aditisjoshi/dankherb/finalCadAndCutFiles/render.JPG

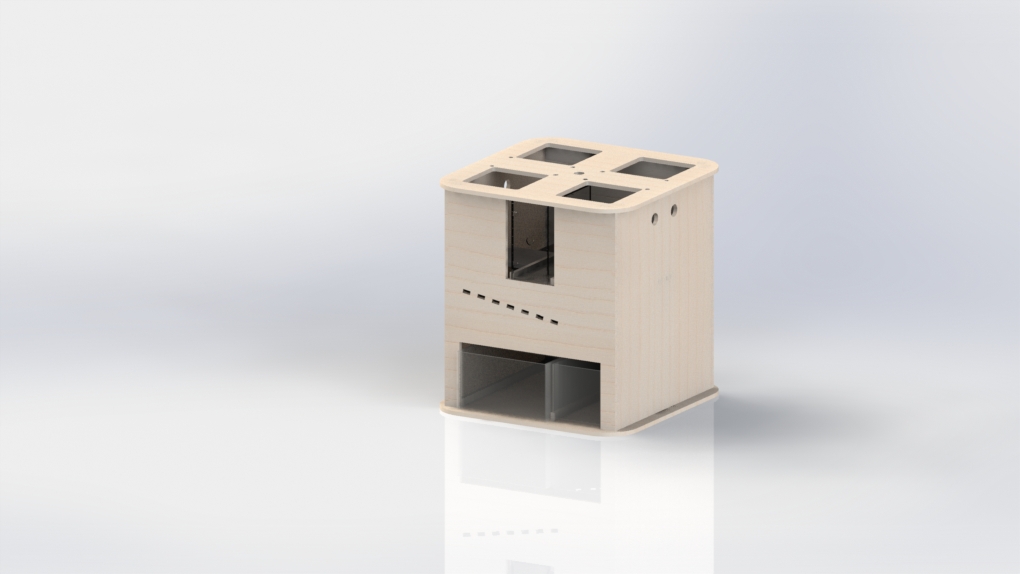
finalCadAndCutFiles/render.JPG
