aditisjoshi/dankherb/sun.png

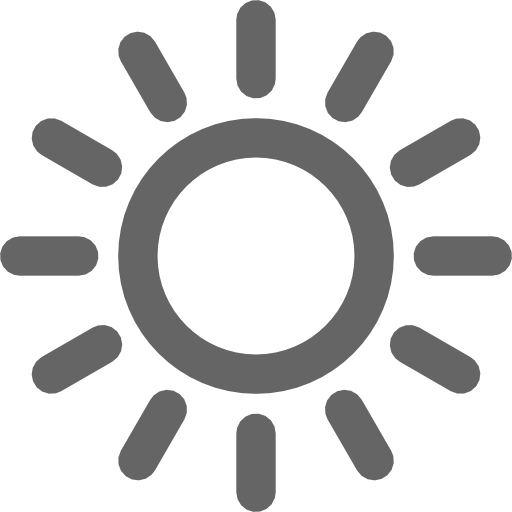
sun.png
