aditisjoshi/dankherb/water.png

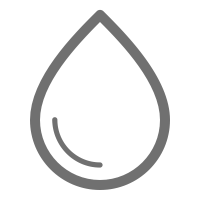
water.png
