aditisjoshi/dankherb/website/images/2sateAaron.png

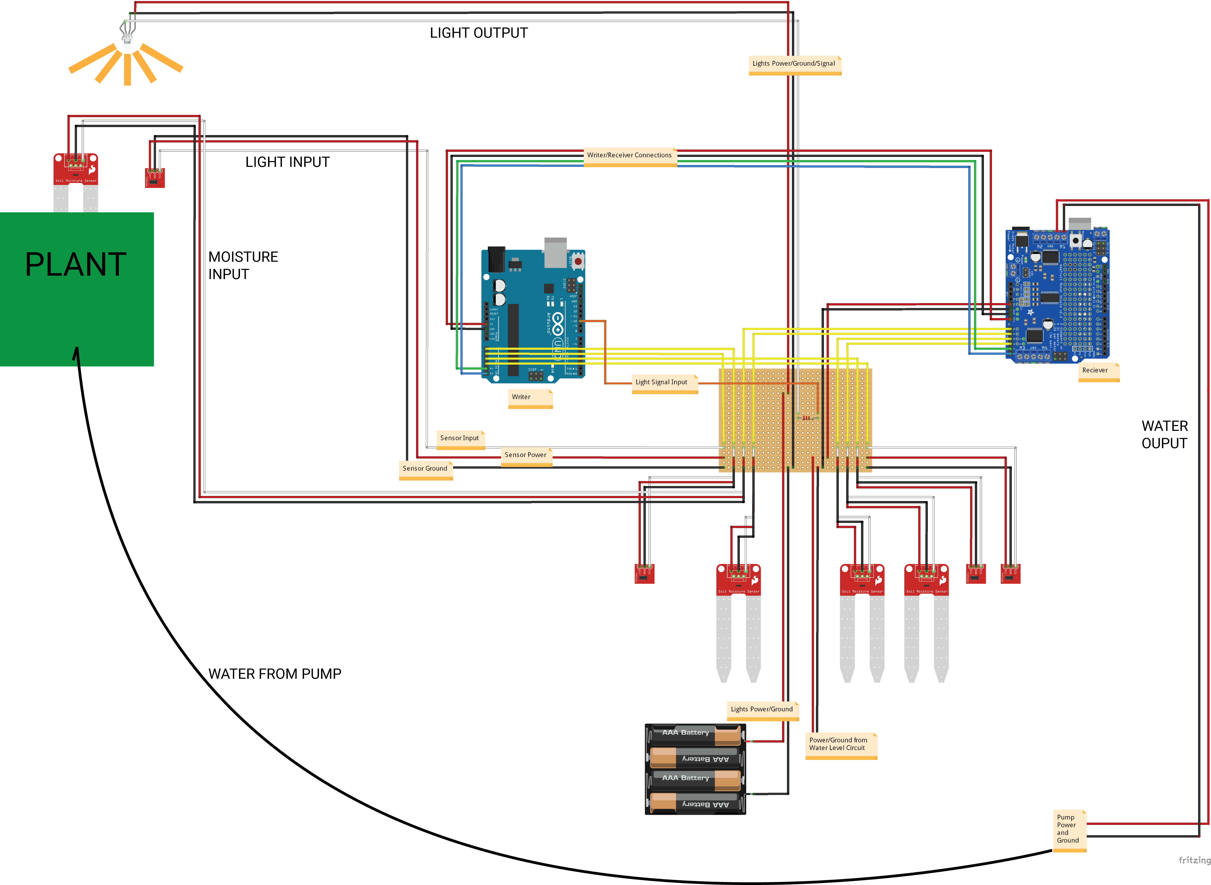
website/images/2sateAaron.png
