aditisjoshi/dankherb/website/images/acrylicboxes.jpg

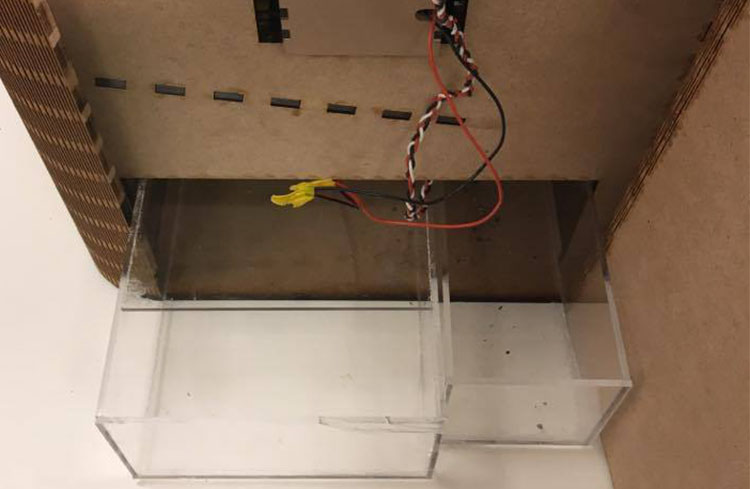
website/images/acrylicboxes.jpg
