aditisjoshi/dankherb/website/images/aditiphoto.JPG

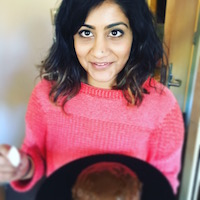
website/images/aditiphoto.JPG
