aditisjoshi/dankherb/website/images/arduinos.jpg

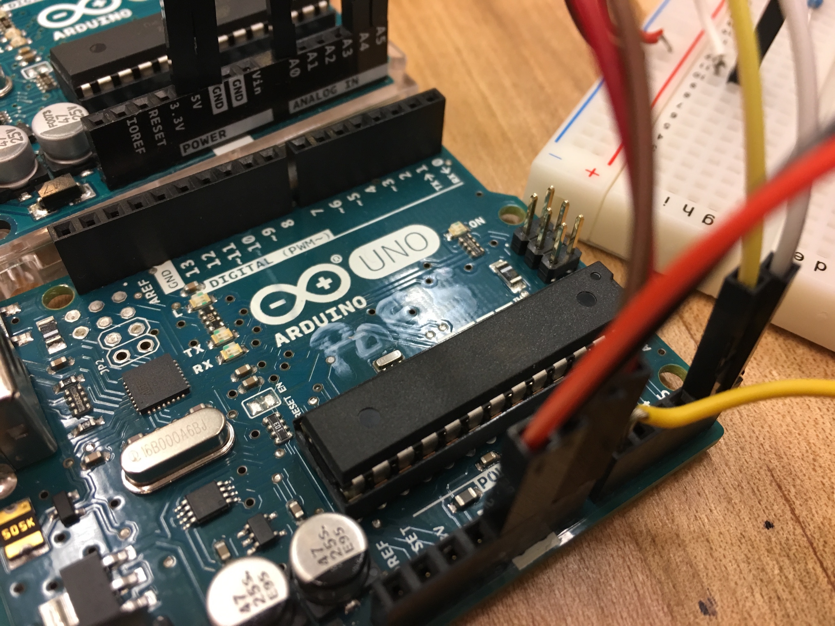
website/images/arduinos.jpg
