aditisjoshi/dankherb/website/images/gallery1.JPG

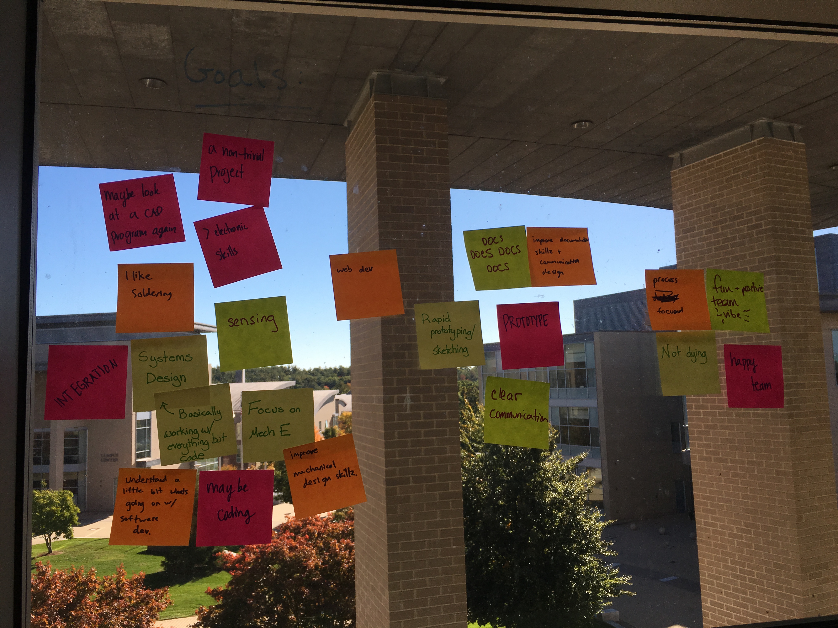
website/images/gallery1.JPG
