aditisjoshi/dankherb/website/images/gallery2.JPG

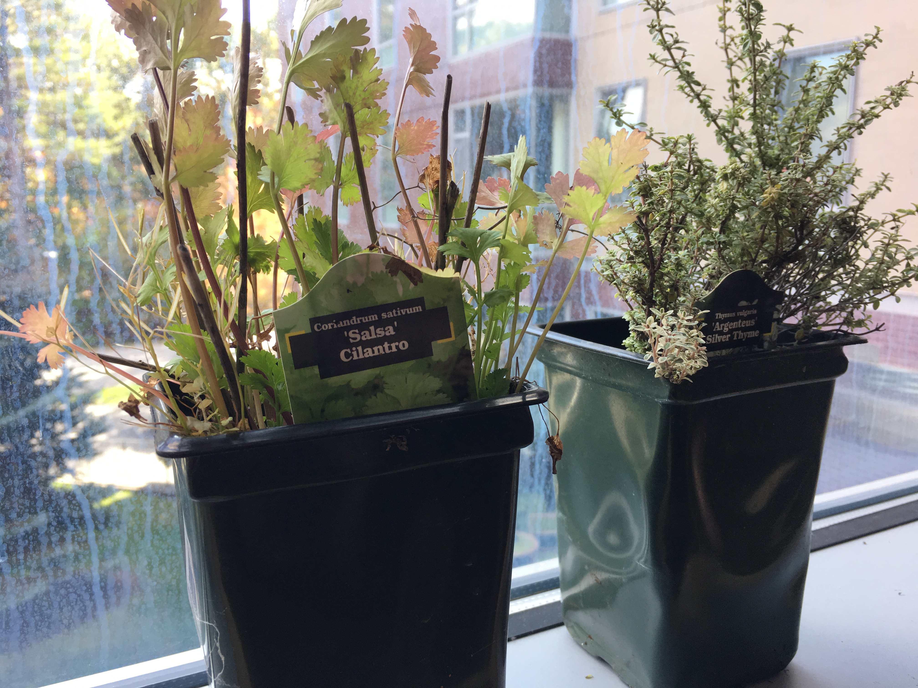
website/images/gallery2.JPG
