aditisjoshi/dankherb/website/images/gallery4.JPG

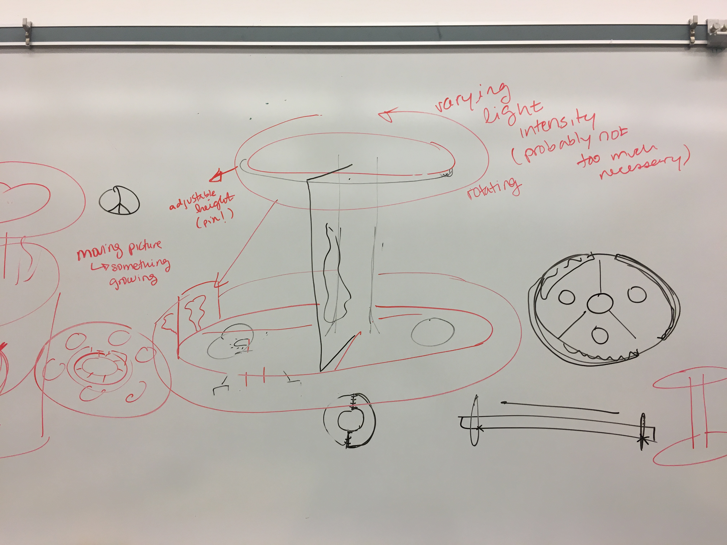
website/images/gallery4.JPG
