aditisjoshi/dankherb/website/images/gallery5.JPG

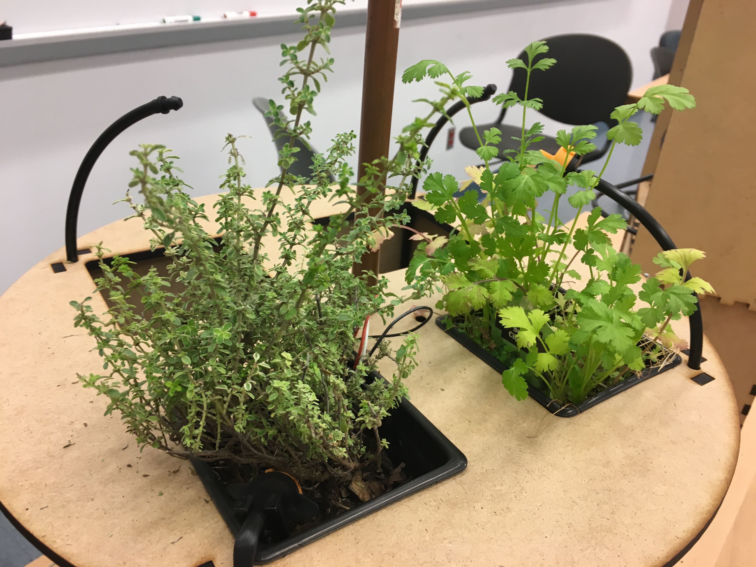
website/images/gallery5.JPG
