aditisjoshi/dankherb/website/images/gallery6.JPG

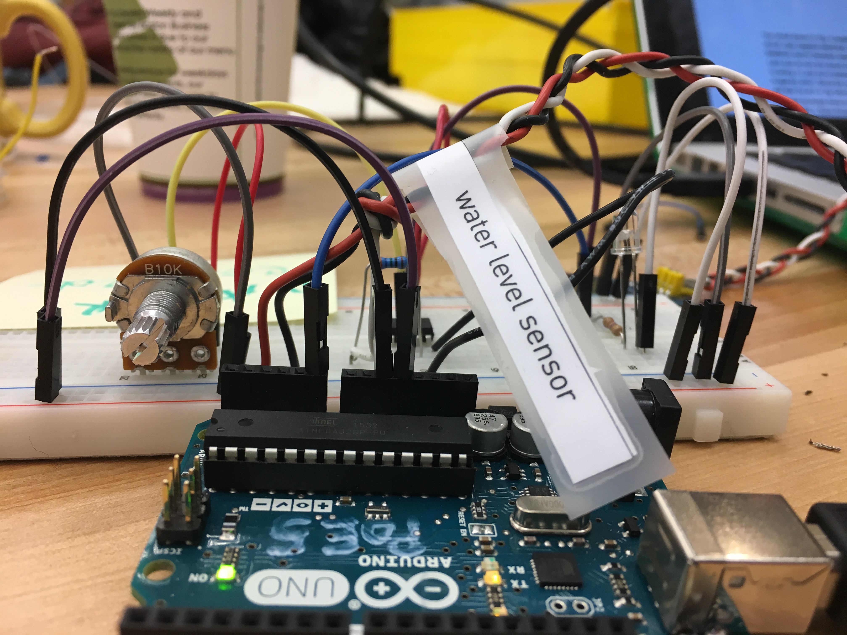
website/images/gallery6.JPG
