aditisjoshi/dankherb/website/images/gallery8.jpg

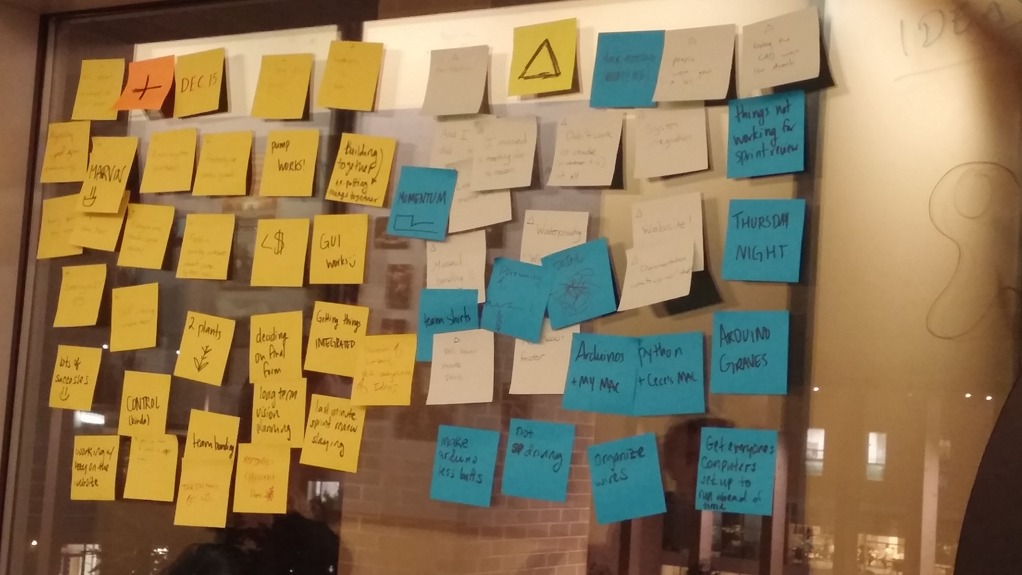
website/images/gallery8.jpg
