aditisjoshi/dankherb/website/images/gallery9.jpg

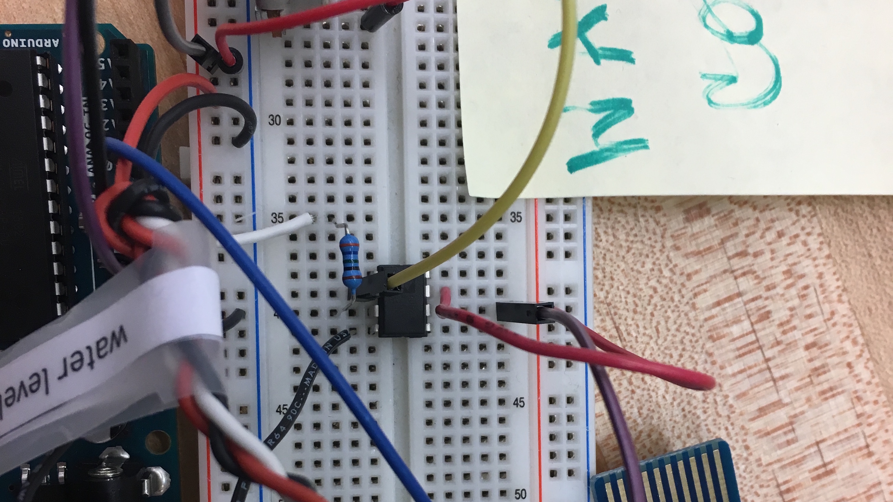
website/images/gallery9.jpg
