aditisjoshi/dankherb/website/images/gallery11.JPG

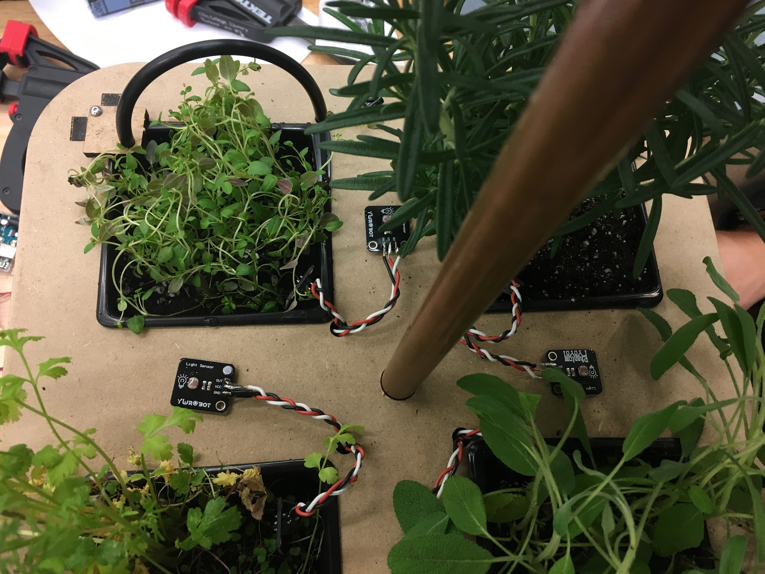
website/images/gallery11.JPG
