aditisjoshi/dankherb/website/images/gallery12.JPG

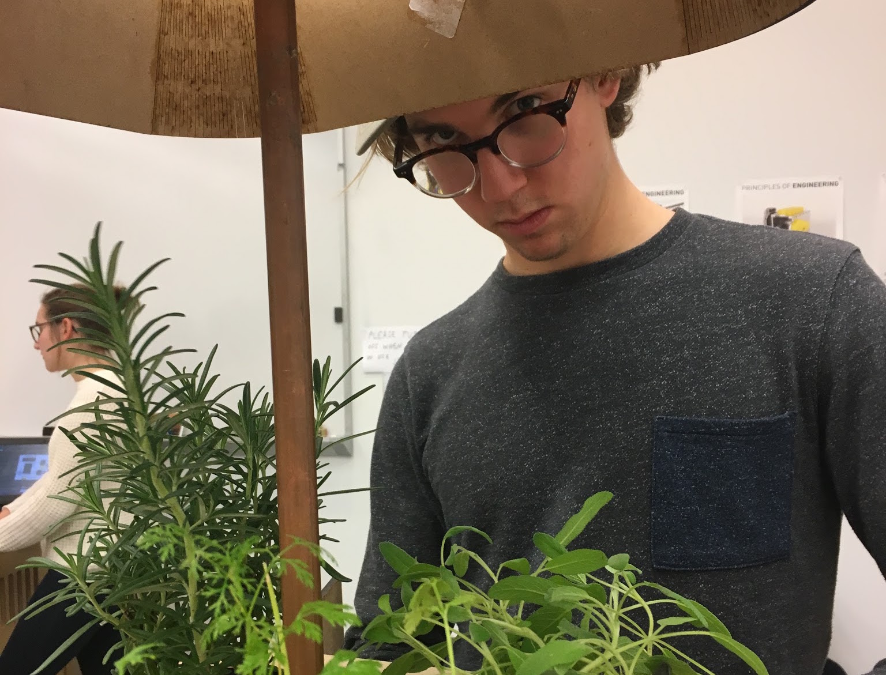
website/images/gallery12.JPG
