aditisjoshi/dankherb/website/images/gallery13.JPG

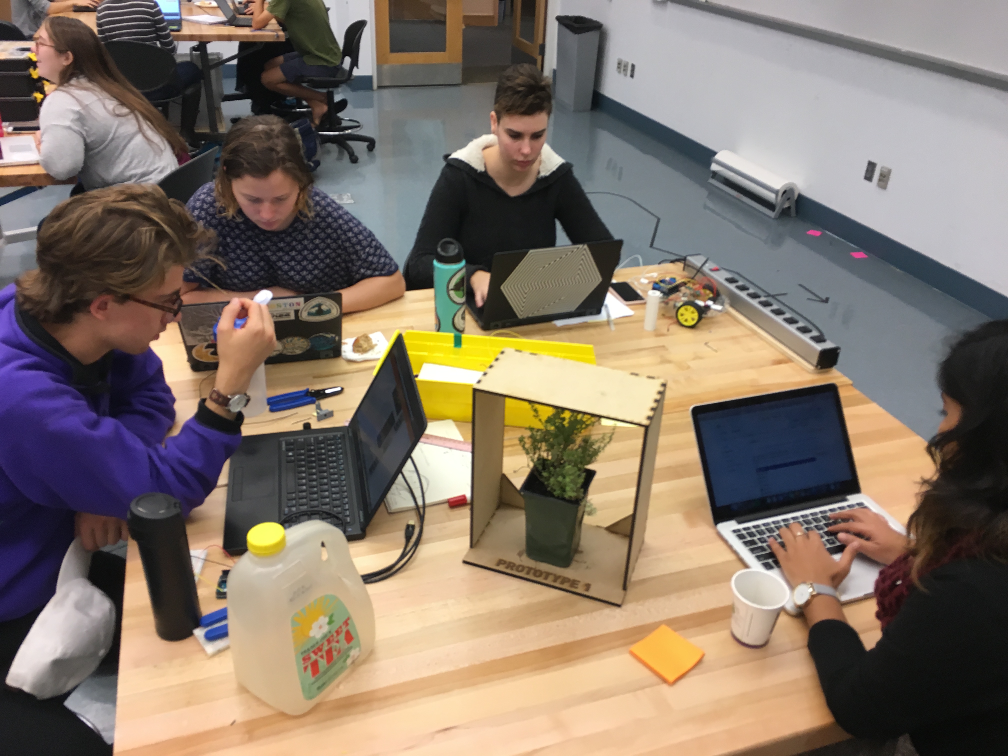
website/images/gallery13.JPG
