aditisjoshi/dankherb/website/images/gallery14.JPG

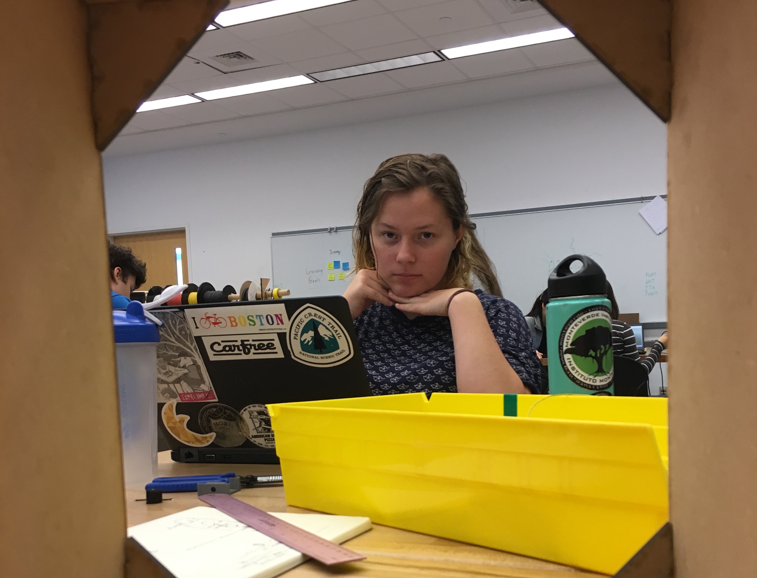
website/images/gallery14.JPG
