aditisjoshi/dankherb/website/images/gallery15.JPG

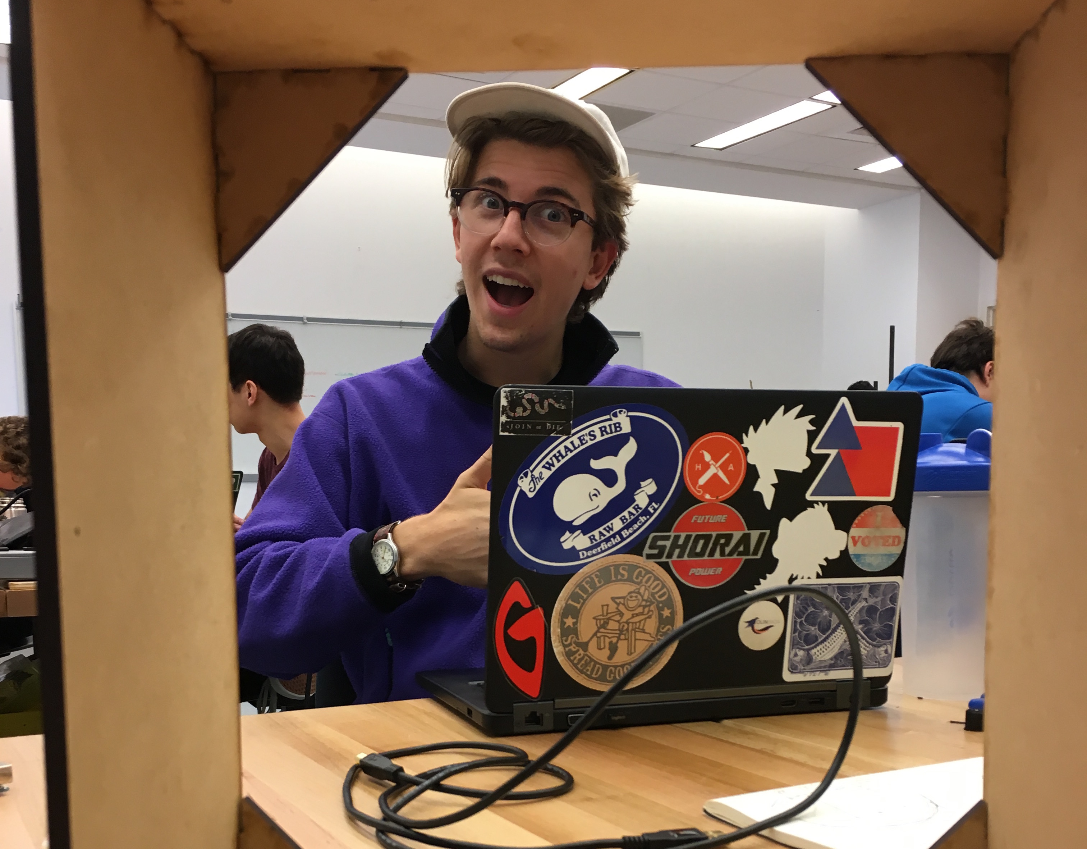
website/images/gallery15.JPG
