aditisjoshi/dankherb/website/images/gallery16.JPG

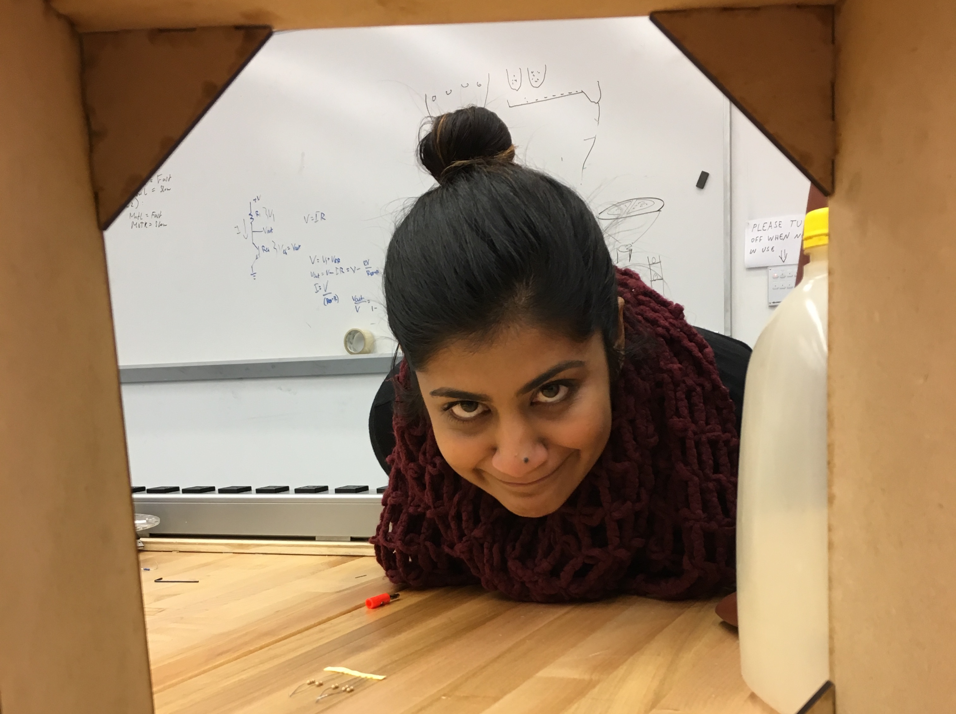
website/images/gallery16.JPG
