aditisjoshi/dankherb/website/images/gallery17.JPG

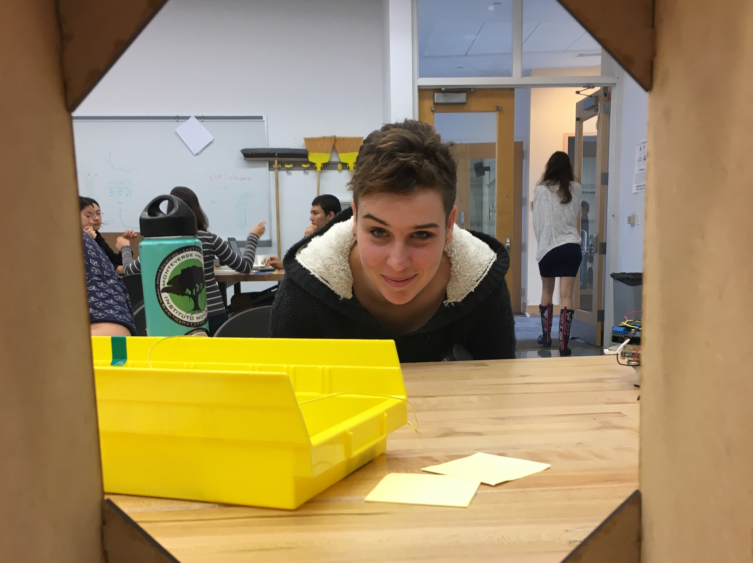
website/images/gallery17.JPG
