aditisjoshi/dankherb/website/images/gallery18.JPG

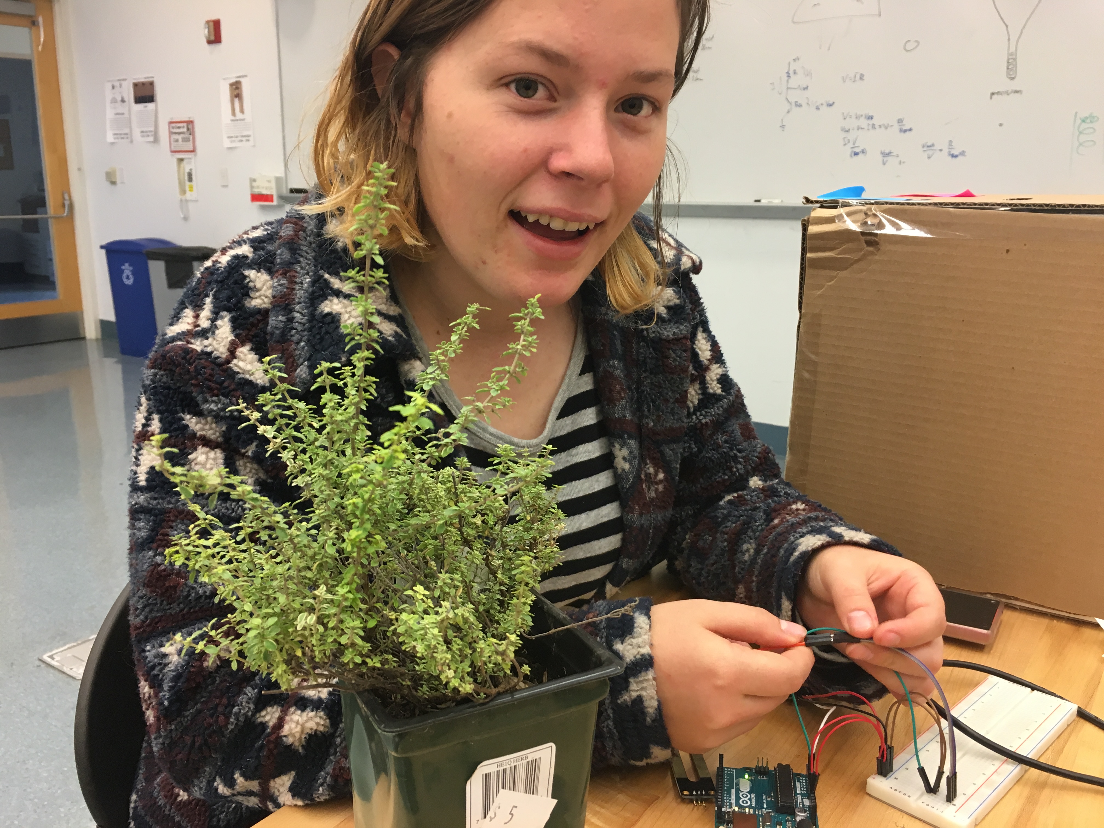
website/images/gallery18.JPG
