aditisjoshi/dankherb/website/images/gallery19.JPG

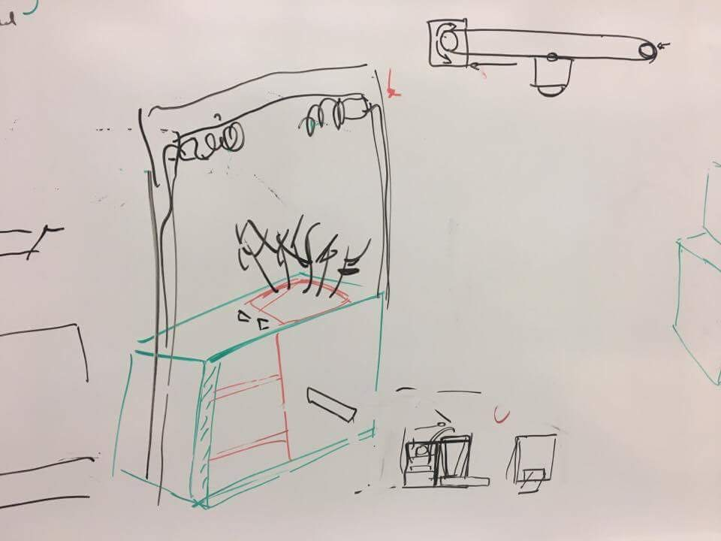
website/images/gallery19.JPG
