aditisjoshi/dankherb/website/images/gallery20.JPG

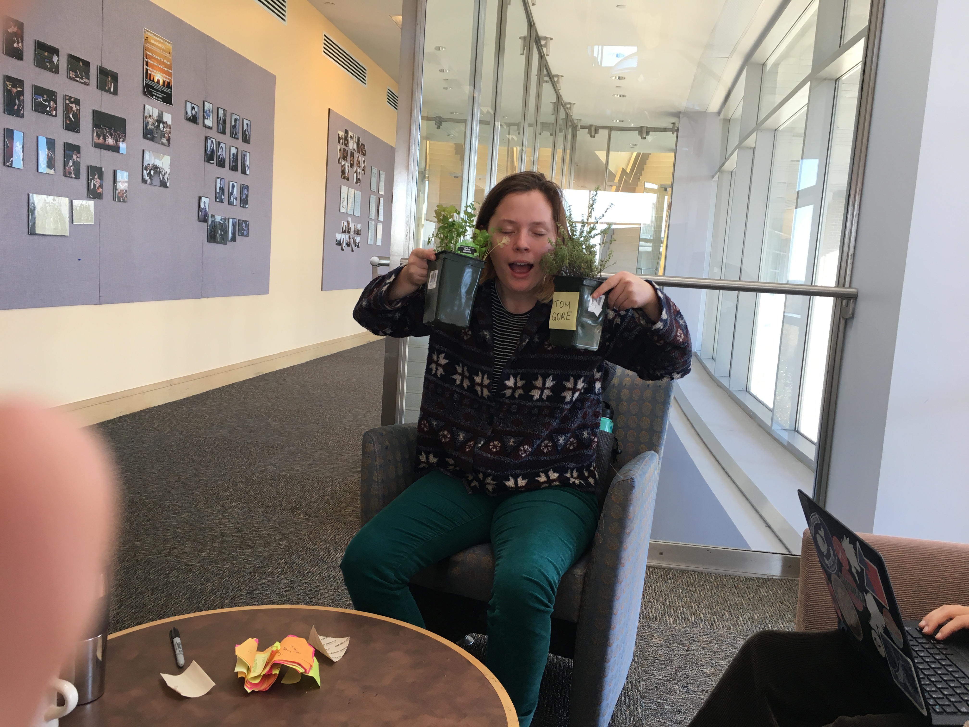
website/images/gallery20.JPG
