aditisjoshi/dankherb/website/images/harperphoto.jpg

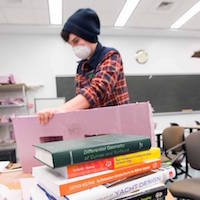
website/images/harperphoto.jpg
