aditisjoshi/dankherb/website/images/hero_image.jpg

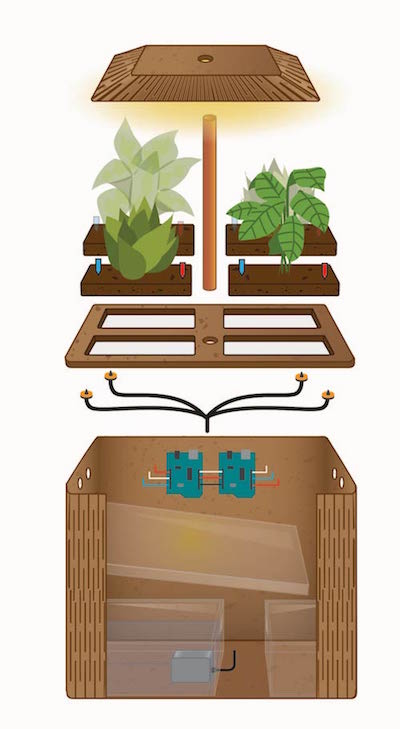
website/images/hero_image.jpg
