aditisjoshi/dankherb/website/images/HeroImageWithCallouts.png

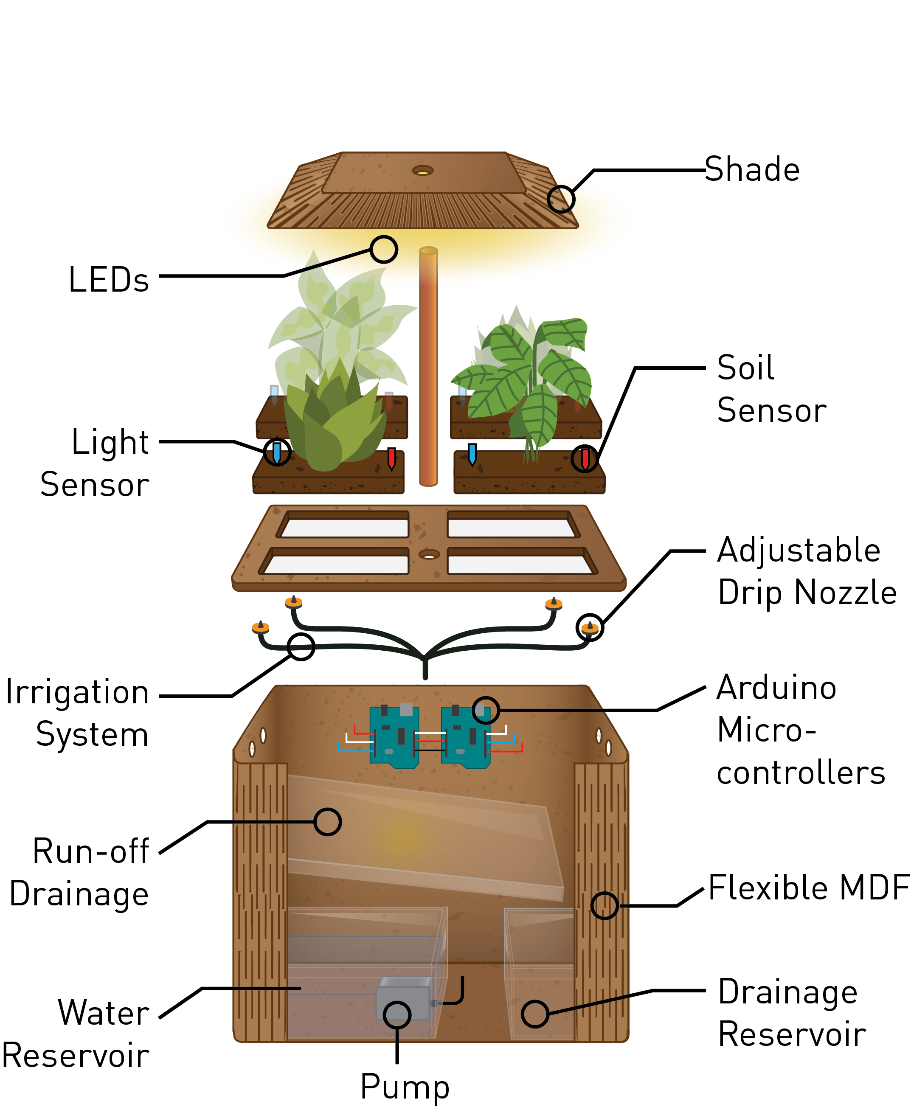
website/images/HeroImageWithCallouts.png
