aditisjoshi/dankherb/website/images/izzyphoto.jpg

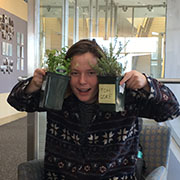
website/images/izzyphoto.jpg
