aditisjoshi/dankherb/website/images/johnphoto.JPG

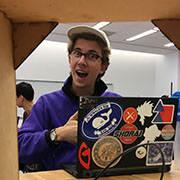
website/images/johnphoto.JPG
