aditisjoshi/dankherb/website/images/mech1.png

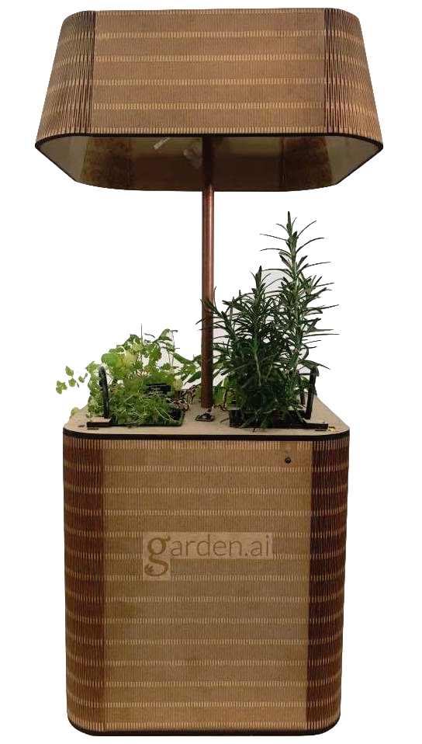
website/images/mech1.png
