aditisjoshi/dankherb/website/images/pump.jpg

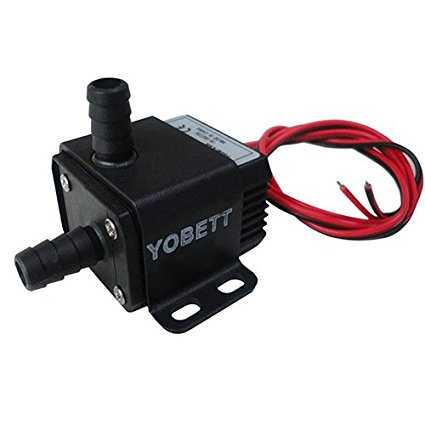
website/images/pump.jpg
