aditisjoshi/dankherb/website/images/python_code.png

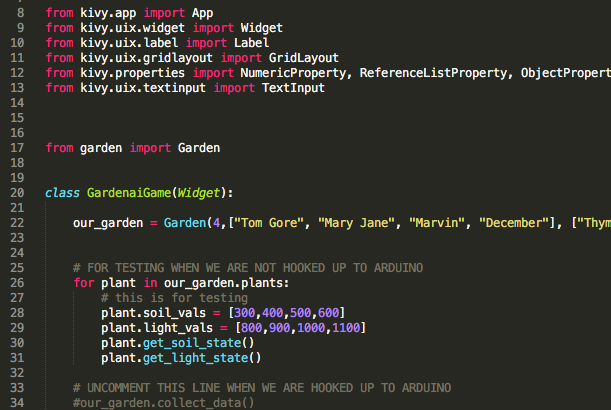
website/images/python_code.png
