aditisjoshi/dankherb/website/images/sprint1.JPG

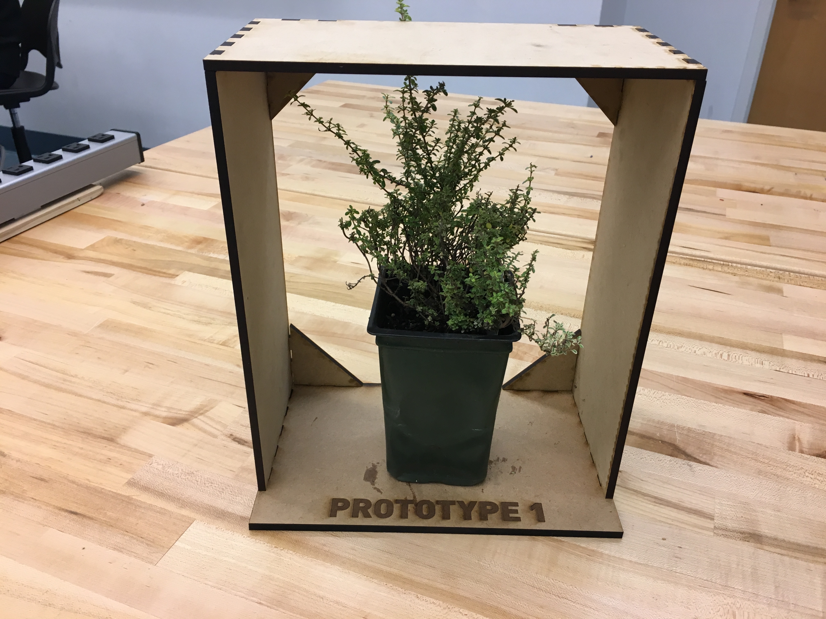
website/images/sprint1.JPG
