aditisjoshi/dankherb/website/images/sprint2.JPG

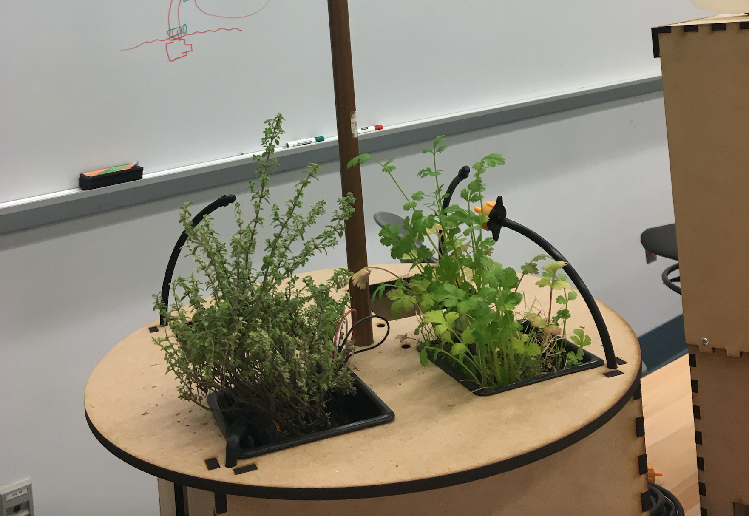
website/images/sprint2.JPG
