aditisjoshi/dankherb/website/images/sprint3.JPG

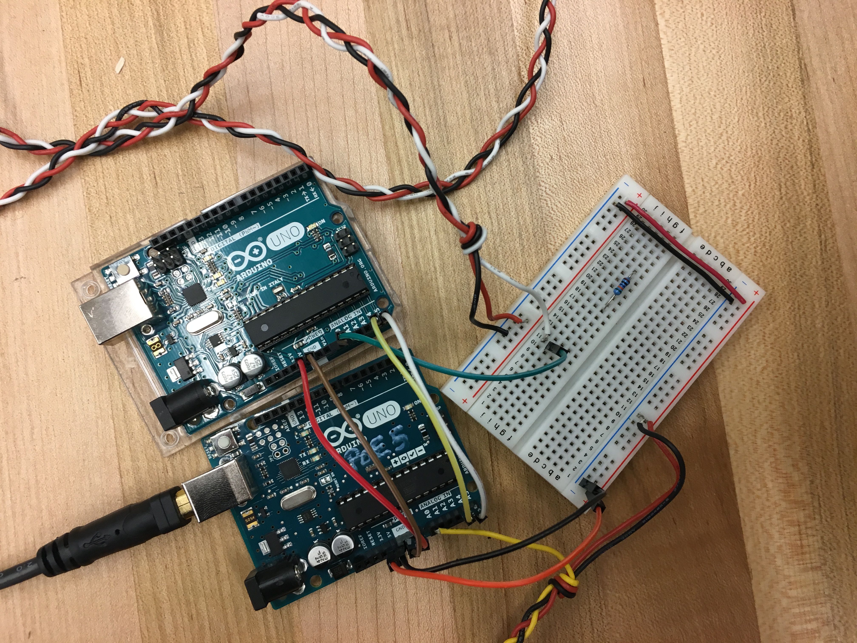
website/images/sprint3.JPG
