aditisjoshi/dankherb/website/images/sprint4.jpg

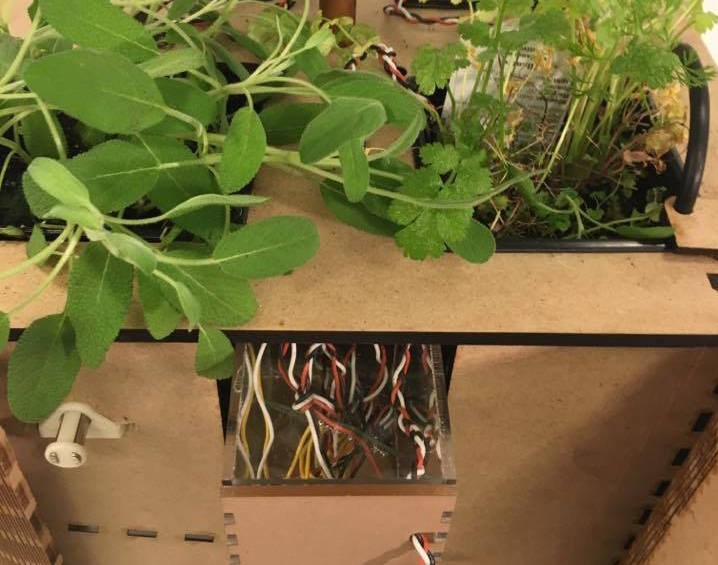
website/images/sprint4.jpg
