aditisjoshi/dankherb/website/images/water_level_sensor.jpg

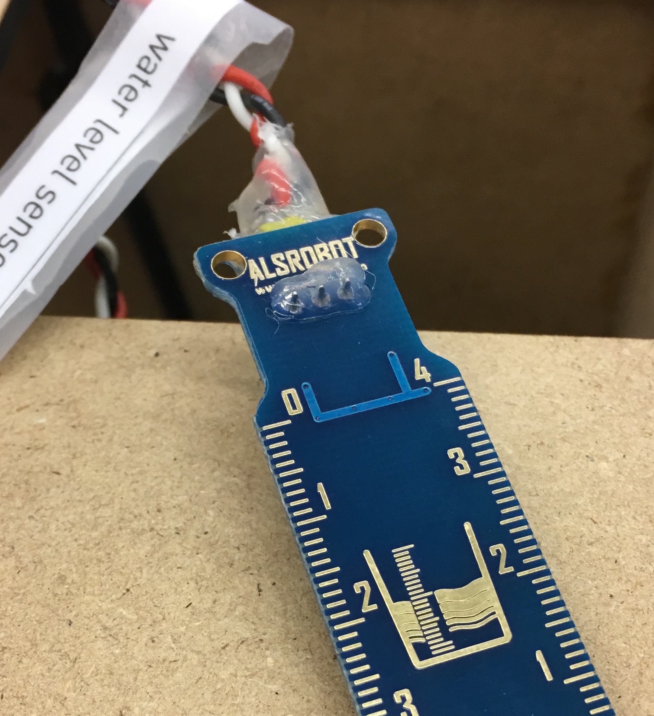
website/images/water_level_sensor.jpg
