aditisjoshi/dankherb/website/images/waterlevelCircuit.jpg

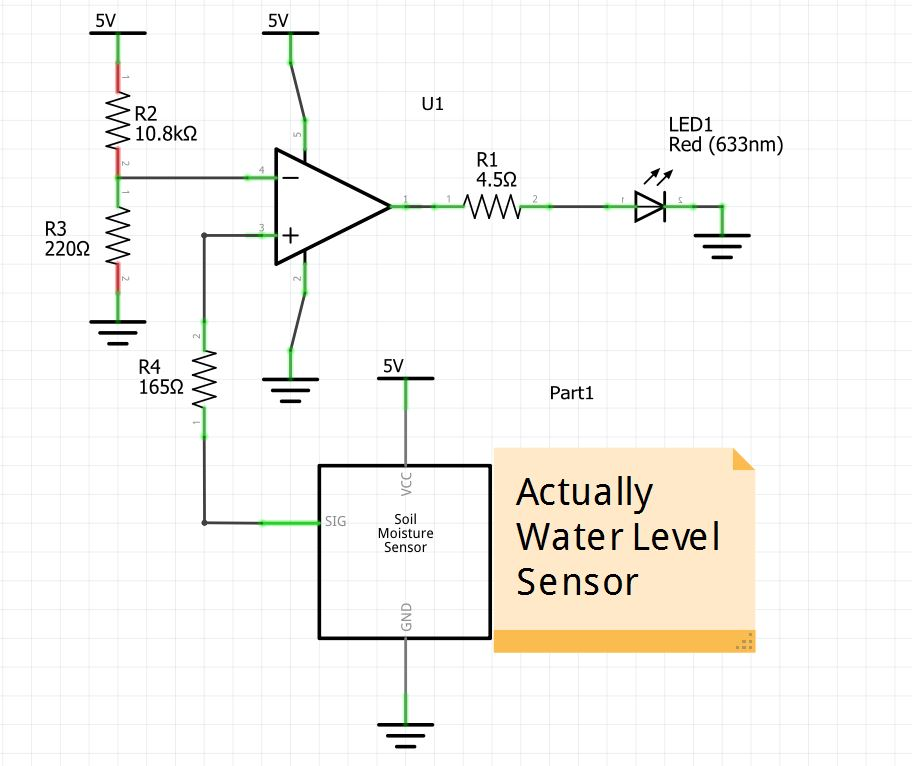
website/images/waterlevelCircuit.jpg
