aditisjoshi/dankherb/finalCadAndCutFiles/electronicsbox/elecback.SLDPRT

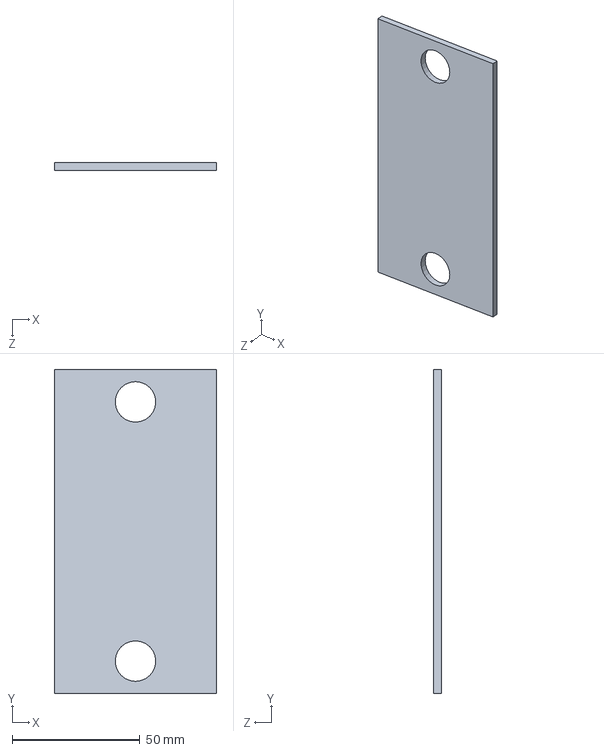
[picture p59: CAD file, 2016-12-13]
finalCadAndCutFiles/electronicsbox/elecback.SLDPRT
63.5 x 127.0 x 3.00 mm
