aditisjoshi/dankherb/finalCadAndCutFiles/main cut sheets/1_4mdf2.DXF

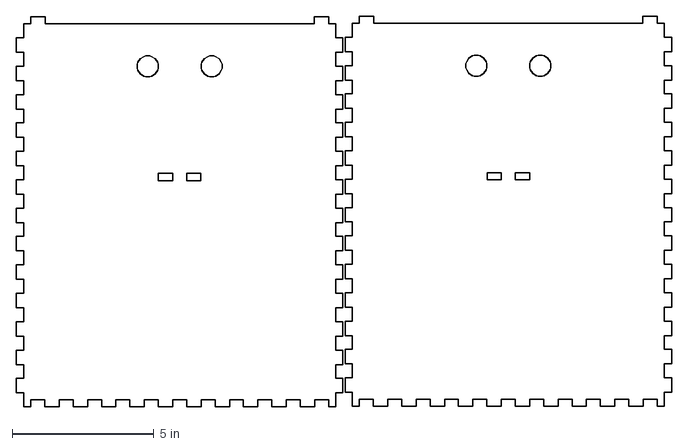
[picture p60: CAD file, 2016-12-13]
finalCadAndCutFiles/main cut sheets/1_4mdf2.DXF
23.1 x 13.8 in
