aditisjoshi/dankherb/finalCadAndCutFiles/ramp.SLDPRT

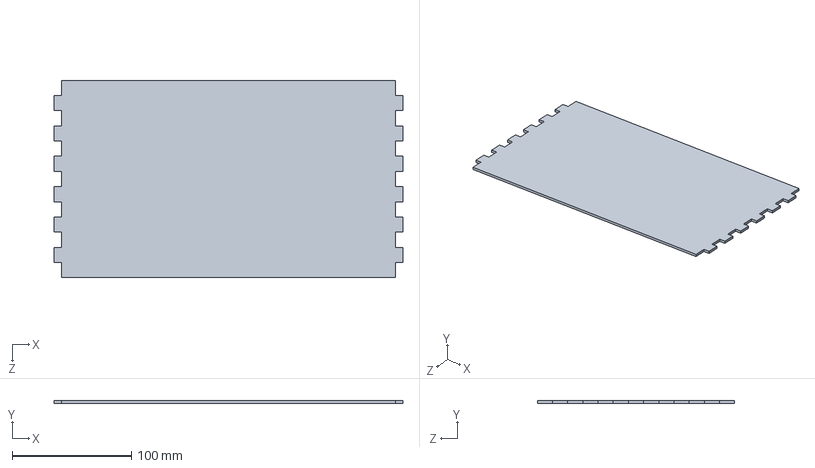
[picture p61: CAD file, 2016-12-13]
finalCadAndCutFiles/ramp.SLDPRT
292.1 x 2.54 x 165.1 mm
