aditisjoshi/dankherb/finalCadAndCutFiles/backpanel.SLDPRT

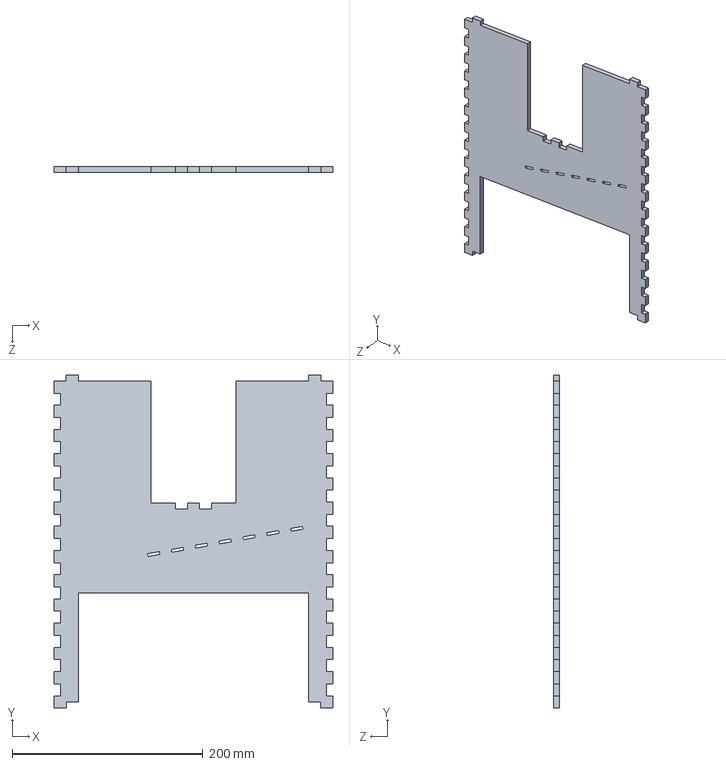
[picture p62: CAD file, 2016-12-13]
finalCadAndCutFiles/backpanel.SLDPRT
292.1 x 349.2 x 6.35 mm
