aditisjoshi/dankherb/finalCadAndCutFiles/drainageresovoir/drbottom.SLDPRT

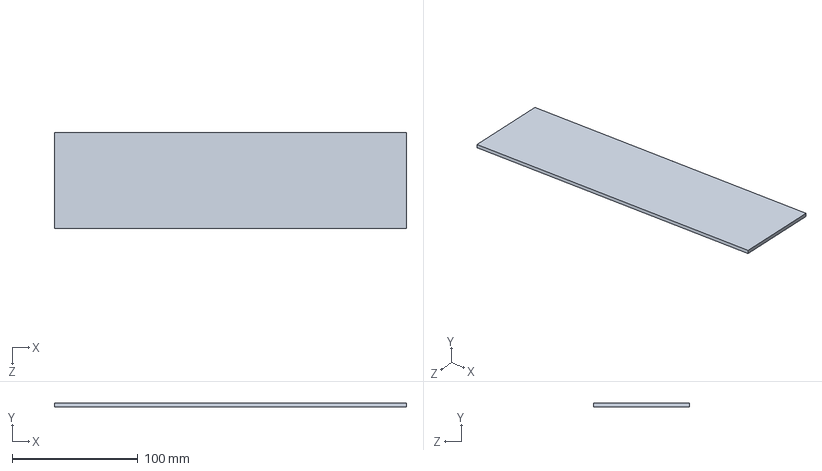
[picture p63: CAD file, 2016-12-13]
finalCadAndCutFiles/drainageresovoir/drbottom.SLDPRT
279.8 x 3.00 x 76.6 mm
