aditisjoshi/dankherb/finalCadAndCutFiles/main cut sheets/118AcrylicRampAndBox.DXF

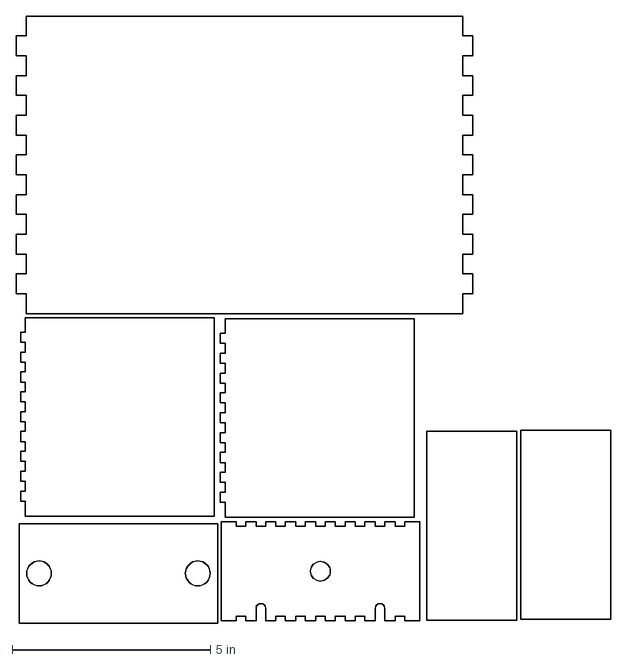
[picture p64: CAD file, 2016-12-13]
finalCadAndCutFiles/main cut sheets/118AcrylicRampAndBox.DXF
15.0 x 15.3 in
