aditisjoshi/dankherb/finalCadAndCutFiles/pump resovoir/waterbottom2.SLDPRT

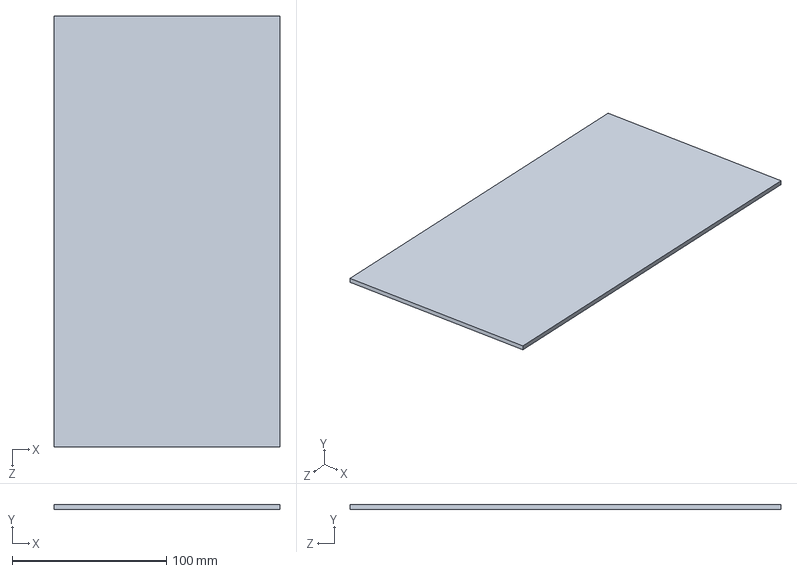
[picture p65: CAD file, 2016-12-13]
finalCadAndCutFiles/pump resovoir/waterbottom2.SLDPRT
146.4 x 3.00 x 279.8 mm
