aditisjoshi/dankherb/finalCadAndCutFiles/electronicsbox/elecbottom.SLDPRT

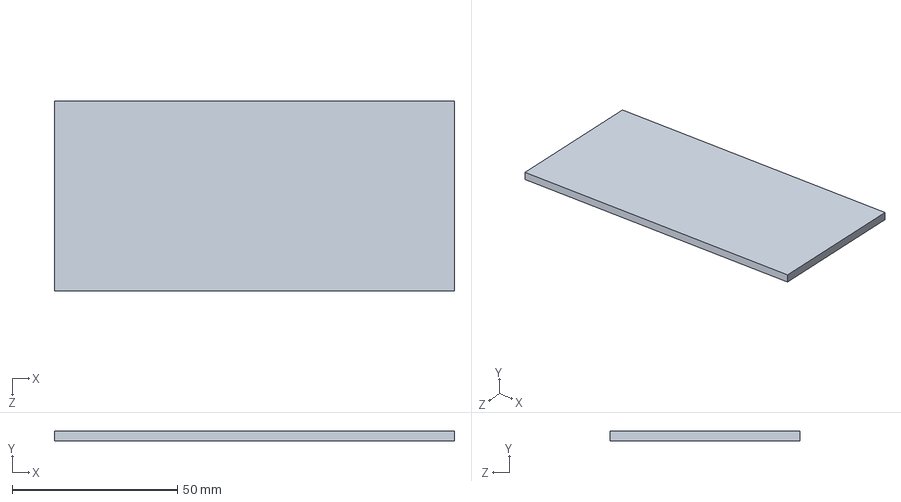
[picture p66: CAD file, 2016-12-13]
finalCadAndCutFiles/electronicsbox/elecbottom.SLDPRT
121.0 x 3.00 x 57.5 mm
