aditisjoshi/dankherb/finalCadAndCutFiles/lightmount.SLDPRT

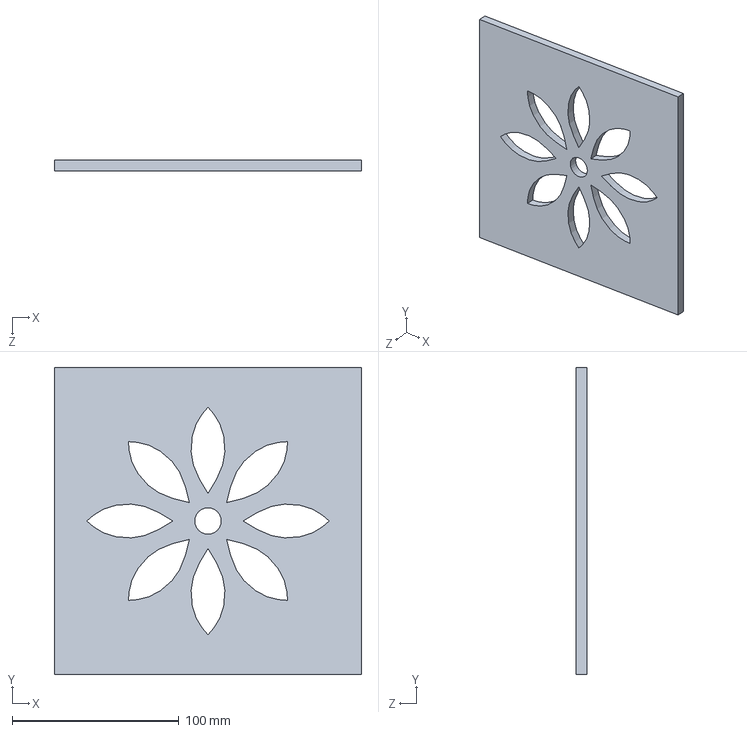
[picture p67: CAD file, 2016-12-13]
finalCadAndCutFiles/lightmount.SLDPRT
184.1 x 184.1 x 6.35 mm
