aditisjoshi/dankherb/finalCadAndCutFiles/main cut sheets/1_4mdf4.DXF

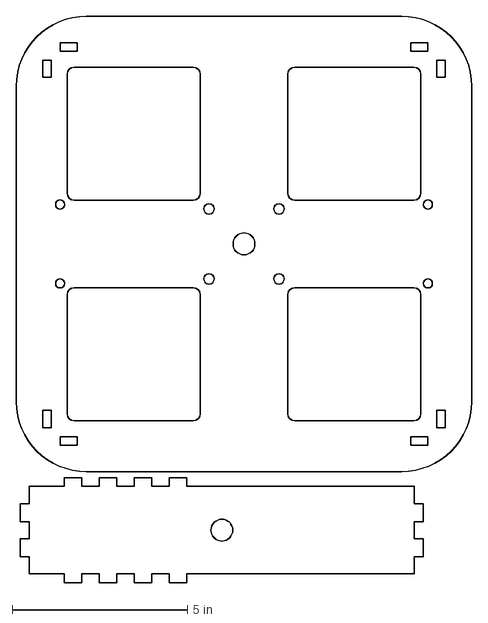
[picture p68: CAD file, 2016-12-13]
finalCadAndCutFiles/main cut sheets/1_4mdf4.DXF
13.0 x 16.2 in
