aditisjoshi/dankherb/finalCadAndCutFiles/pump resovoir/frontandback.SLDPRT

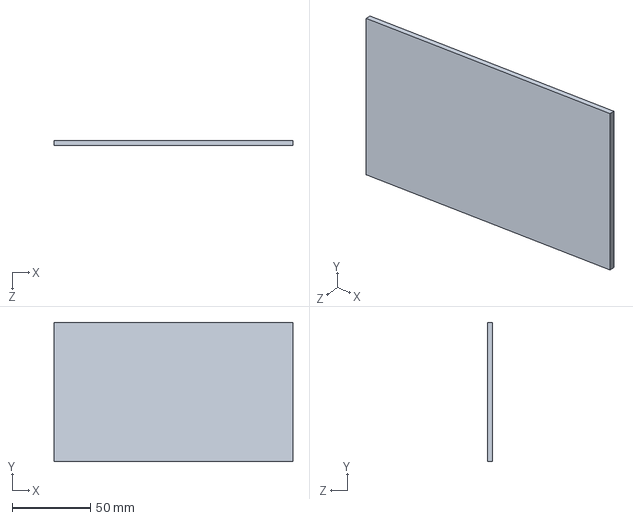
[picture p69: CAD file, 2016-12-13]
finalCadAndCutFiles/pump resovoir/frontandback.SLDPRT
152.4 x 88.9 x 3.00 mm
