aditisjoshi/dankherb/finalCadAndCutFiles/main cut sheets/1_4mdf3.DXF

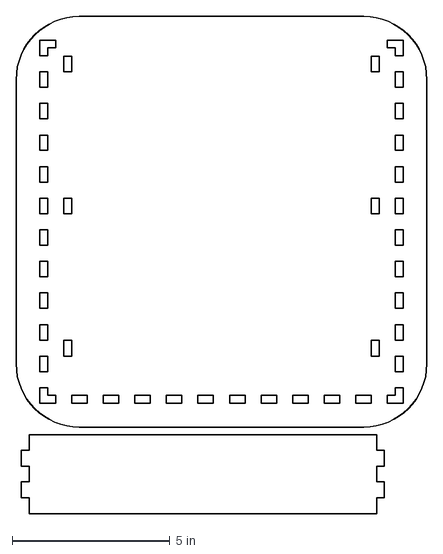
[picture p70: CAD file, 2016-12-13]
finalCadAndCutFiles/main cut sheets/1_4mdf3.DXF
13.0 x 15.7 in
