aditisjoshi/dankherb/finalCadAndCutFiles/boxrails.SLDPRT

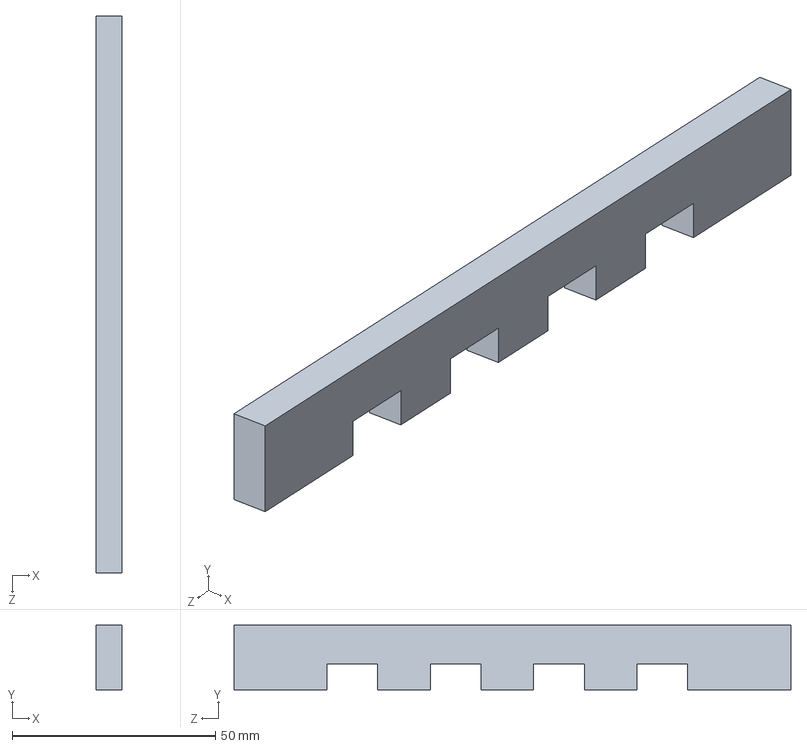
[picture p71: CAD file, 2016-12-13]
finalCadAndCutFiles/boxrails.SLDPRT
6.35 x 15.9 x 136.9 mm
