aditisjoshi/dankherb/finalCadAndCutFiles/coppertube.SLDPRT

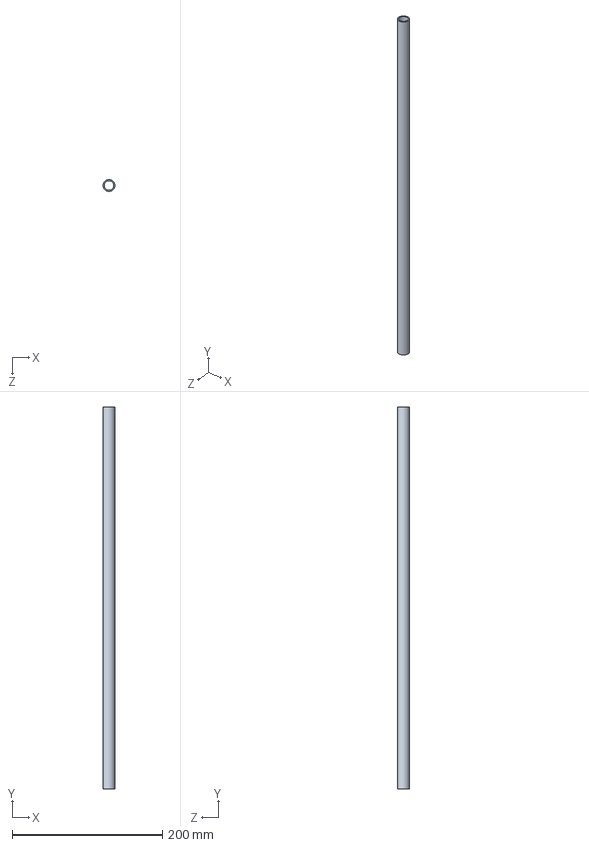
[picture p72: CAD file, 2016-12-13]
finalCadAndCutFiles/coppertube.SLDPRT
15.9 x 508.0 x 15.9 mm
