aditisjoshi/dankherb/finalCadAndCutFiles/sidepanel2.SLDPRT

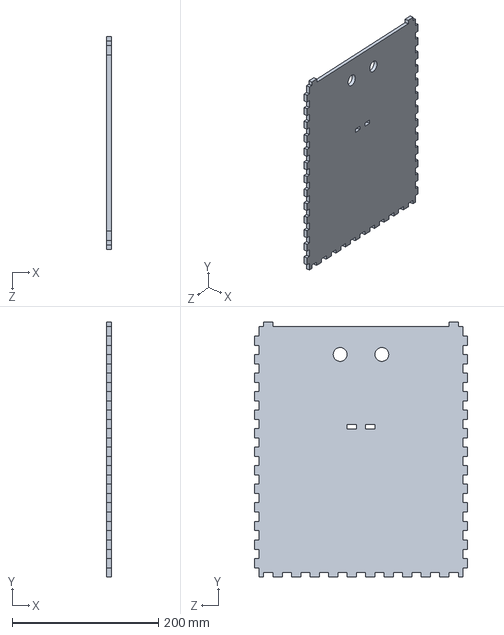
[picture p73: CAD file, 2016-12-13]
finalCadAndCutFiles/sidepanel2.SLDPRT
6.35 x 349.2 x 292.1 mm
