aditisjoshi/dankherb/finalCadAndCutFiles/bottomstrut.SLDPRT

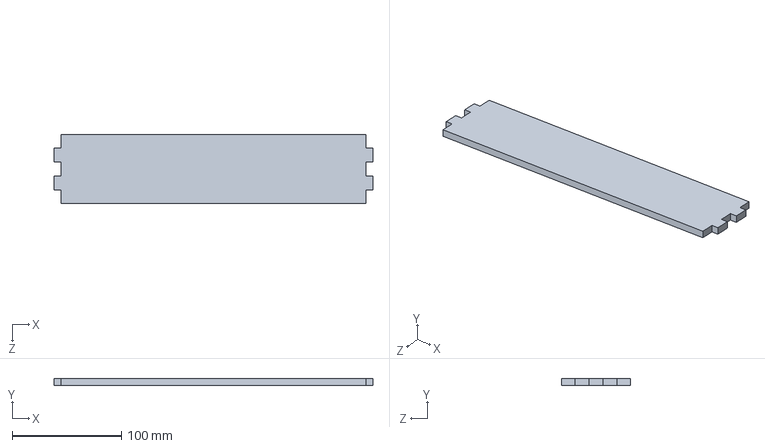
[picture p74: CAD file, 2016-12-13]
finalCadAndCutFiles/bottomstrut.SLDPRT
292.1 x 6.35 x 63.5 mm
