aditisjoshi/dankherb/finalCadAndCutFiles/topstrut2.SLDPRT

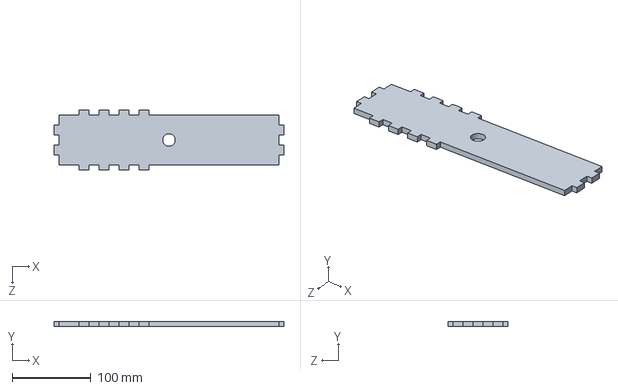
[picture p75: CAD file, 2016-12-13]
finalCadAndCutFiles/topstrut2.SLDPRT
292.1 x 6.35 x 76.2 mm
