aditisjoshi/dankherb/finalCadAndCutFiles/toppanel3.SLDPRT

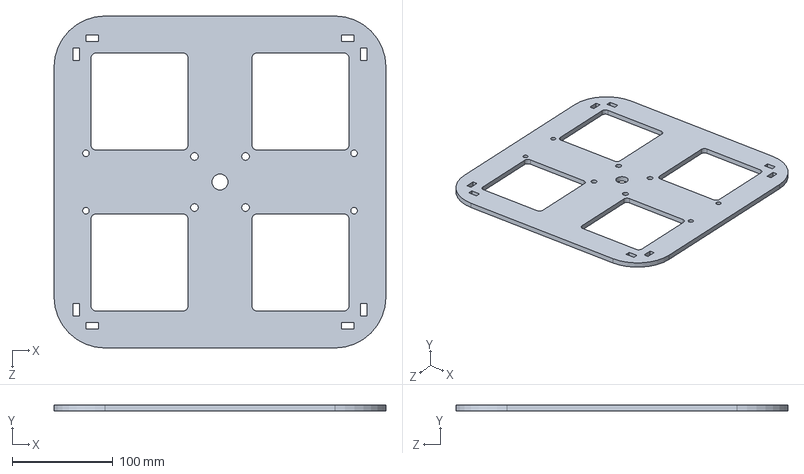
[picture p76: CAD file, 2016-12-13]
finalCadAndCutFiles/toppanel3.SLDPRT
330.2 x 6.35 x 330.2 mm
