aditisjoshi/dankherb/finalCadAndCutFiles/slide.SLDPRT

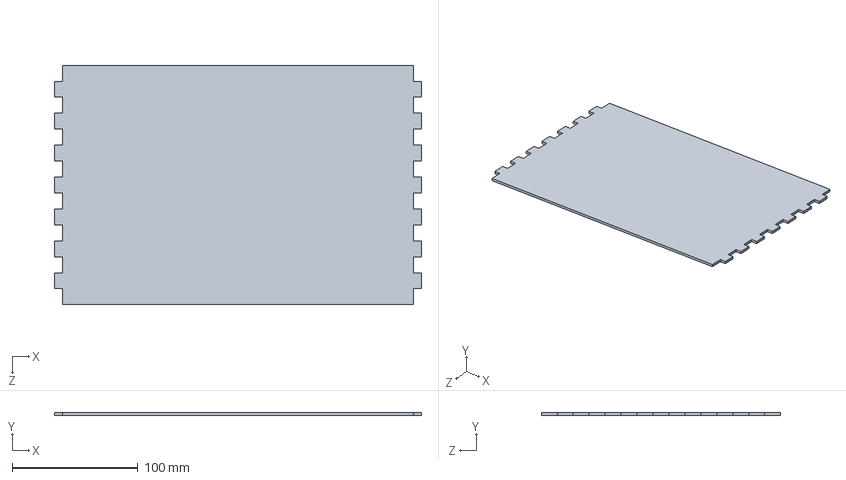
[picture p77: CAD file, 2016-12-13]
finalCadAndCutFiles/slide.SLDPRT
292.1 x 2.54 x 190.5 mm
