aditisjoshi/dankherb/finalCadAndCutFiles/bottom.SLDPRT

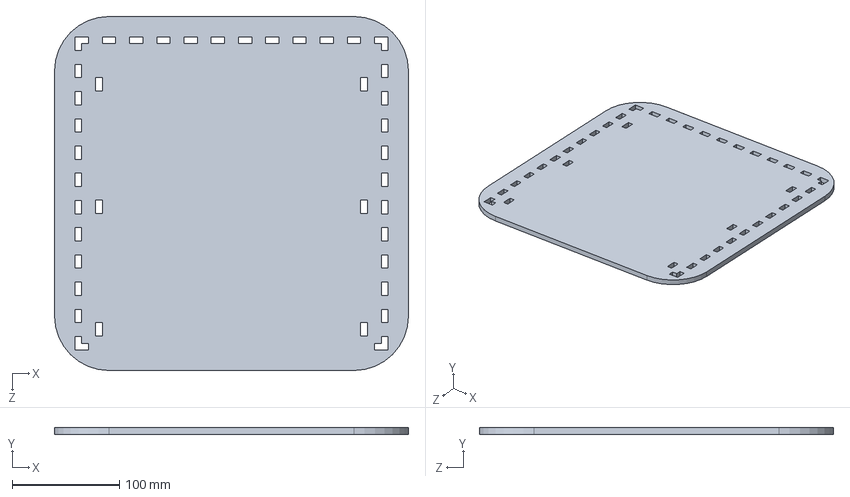
[picture p78: CAD file, 2016-12-13]
finalCadAndCutFiles/bottom.SLDPRT
330.2 x 6.35 x 330.2 mm
